louib/TStick/Eagle Libraries/PCB_board_20190523141823.png

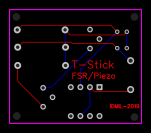
Eagle Libraries/PCB_board_20190523141823.png
