louib/TStick/Sopranino/2GW/FW19101/Docs/images/SopraninoJumperC-uC.jpg

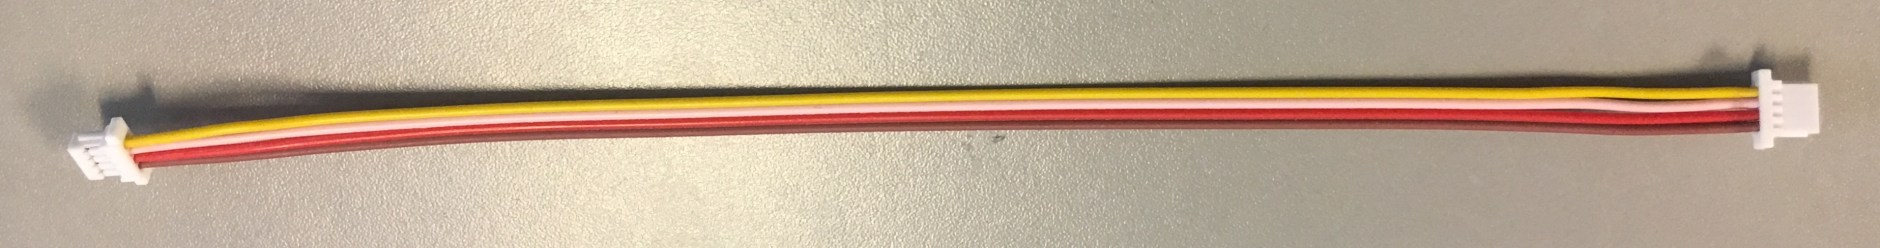
Sopranino/2GW/FW19101/Docs/images/SopraninoJumperC-uC.jpg
