louib/TStick/Sopranino/2GW/FW19101/Docs/MUMT620-t-stick_files/377761_352299741517825_1272722406_n.jpg

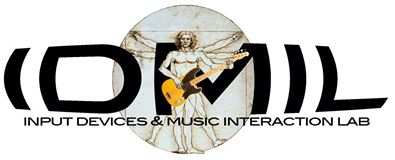
Sopranino/2GW/FW19101/Docs/MUMT620-t-stick_files/377761_352299741517825_1272722406_n.jpg
