louib/TStick/Sopranino/2GW/FW19101/Docs/MUMT620-t-stick_files/19886726_6071430966470_6630702371355754496_n.png.jpg

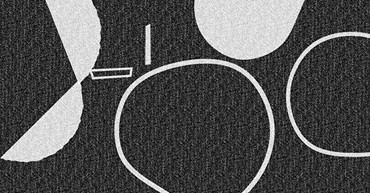
Sopranino/2GW/FW19101/Docs/MUMT620-t-stick_files/19886726_6071430966470_6630702371355754496_n.png.jpg
