louib/TStick/Sopranino/2GW/FW19101/Docs/MUMT620-t-stick_files/29963987_23842841834940019_1535957592986091520_n.png.jpg

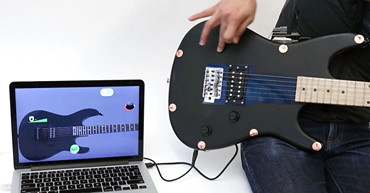
Sopranino/2GW/FW19101/Docs/MUMT620-t-stick_files/29963987_23842841834940019_1535957592986091520_n.png.jpg
