louib/TStick/Sopranino/2GW/FW19101/Docs/MUMT620-t-stick_files/SopraninoWiFi2019.jpg

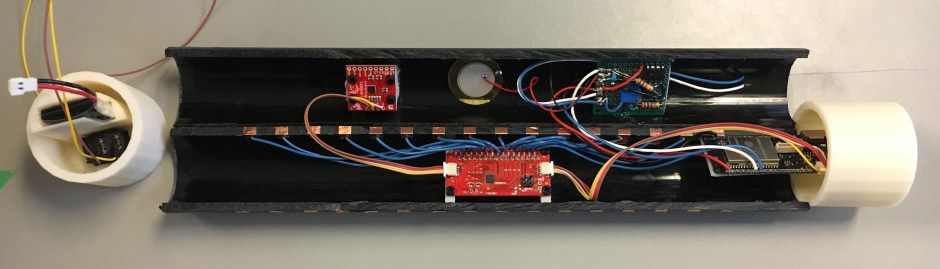
Sopranino/2GW/FW19101/Docs/MUMT620-t-stick_files/SopraninoWiFi2019.jpg
