louib/TStick/Sopranino/2G/172/Sopranino2G-172.sch

## EAGLE design Sopranino/2G/172/Sopranino2G-172.sch (2018-10-29)

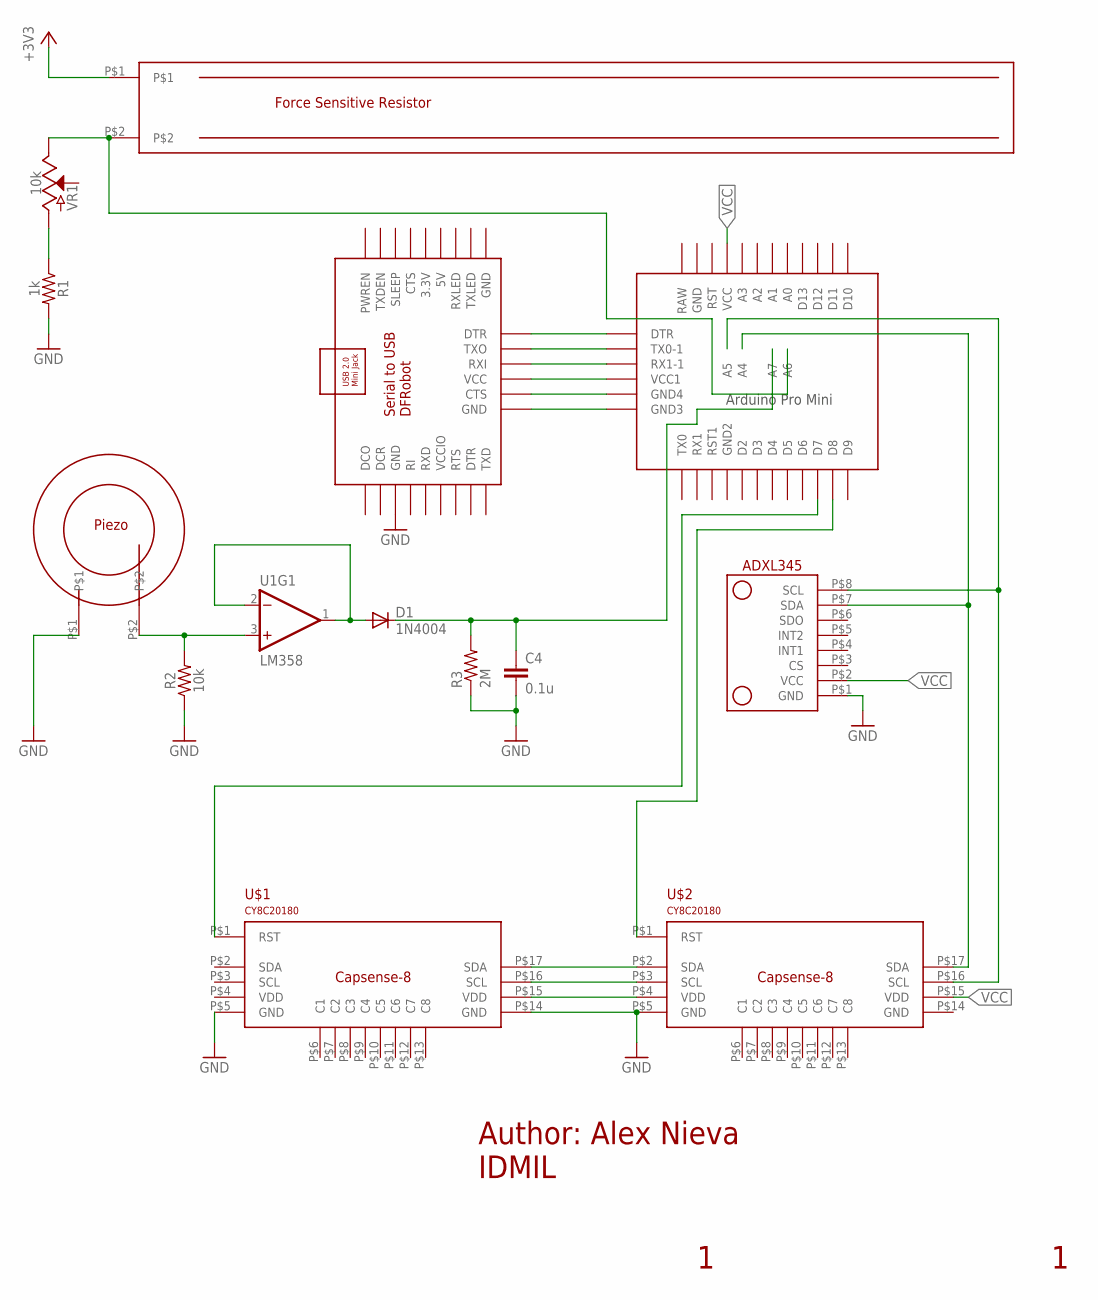
[picture p51: schematic Sopranino2G-172.sch]

Parts:
C4: 0.1u; C5B5.5
D1: 1N4004; DO41-10
R1: 1k; AXIAL-0.3
R2: 10k; AXIAL-0.3
R3: 2M; 0204/7
U1: LM358; DIP08
U$1, U$2: CAPSENSE-8
U$3: ADXL345
U$4: PRO-MINI-2
U$5: FSR_T-STICK
U$7: PIEZO_TSTICK
VR1: 10k; POT-PTH-ALPS

Connections:
+3V3: U$5.P$1
GND: C4.2, R1.P$2 (2), R2.P$1 (1), R3.1, U$1.P$5 (GND), U$1.P$14 (GND), U$2.P$5 (GND), U$3.P$1 (GND), U$7.P$1
unnamed: U$1.P$1 (RST), U$4.D7
unnamed: D1.A, U1.1 (OUT), U1.2 (-IN)
unnamed: U$1.P$17 (SDA), U$2.P$2 (SDA)
unnamed: U$2.P$1 (RST), U$4.D8
unnamed: U$1.P$16 (SCL), U$2.P$3 (SCL)
unnamed: U$1.P$15 (VDD), U$2.P$4 (VDD)
unnamed: R1.P$1 (1), VR1.P$3 (A)
unnamed: U$4.A6, U$5.P$2, VR1.P$1 (E)
unnamed: C4.1, D1.C, R3.2, U$4.A7
unnamed: R2.P$2 (2), U1.3 (+IN), U$7.P$2
SCL: U$2.P$16 (SCL), U$3.P$8 (SCL), U$4.A5
SDA: U$2.P$17 (SDA), U$3.P$7 (SDA), U$4.A4
VCC: U$2.P$15 (VDD), U$3.P$2 (VCC), U$4.VCC

Notes on the sheet:
Author: Alex Nieva IDMIL
