louib/TStick/Sopranino/2GW/FW19021/Sopranino2GW-181.sch

## EAGLE design Sopranino/2GW/FW19021/Sopranino2GW-181.sch (2018-10-29)

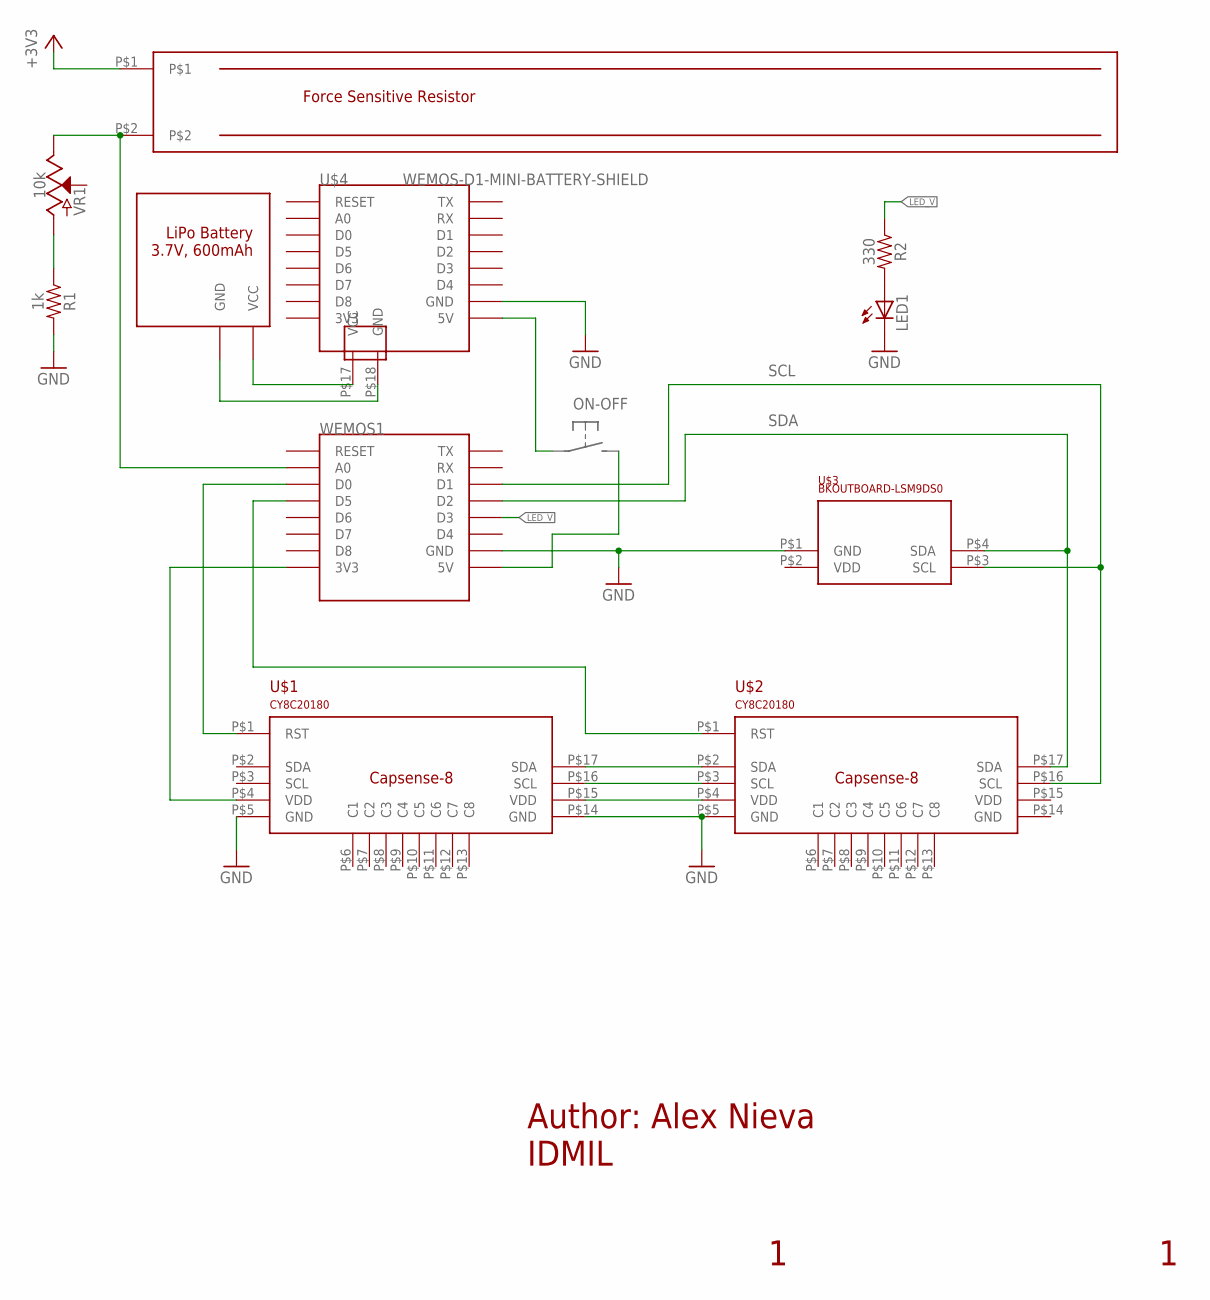
[picture p52: schematic Sopranino2GW-181.sch]

Parts:
LED1: LED3MM
R1: 1k; AXIAL-0.3
R2: 330; AXIAL-0.3
U$1, U$2: CAPSENSE-8
U$3: LSM9DS0_IDMIL_BKOUTBOARD
U$4: WEMOS-D1-MINI-BATTERY-SHIELD
U$5: FSR_T-STICK
VR1: 10k; POT-PTH-ALPS
WEMOS1: WEMOS-D1-MINI

Connections:
+3V3: U$5.P$1
GND: LED1.K (C), R1.P$2 (2), U$1.P$5 (GND), U$1.P$14 (GND), U$2.P$5 (GND), U$3.P$1 (GND), U$4.P$10 (GND), WEMOS1.GND
LED_V: R2.P$1 (1), WEMOS1.D3
unnamed: U$1.P$1 (RST), WEMOS1.D0
unnamed: U$2.P$1 (RST), WEMOS1.D5
unnamed: U$1.P$17 (SDA), U$2.P$2 (SDA)
unnamed: U$1.P$4 (VDD), WEMOS1.3V3
unnamed: U$1.P$16 (SCL), U$2.P$3 (SCL)
unnamed: U$1.P$15 (VDD), U$2.P$4 (VDD)
unnamed: LED1.A, R2.P$2 (2)
unnamed: R1.P$1 (1), VR1.P$3 (A)
unnamed: U$5.P$2, VR1.P$1 (E), WEMOS1.A0
SCL: U$2.P$16 (SCL), U$3.P$3 (SCL), WEMOS1.D1
SDA: U$2.P$17 (SDA), U$3.P$4 (SDA), WEMOS1.D2

Notes on the sheet:
Author: Alex Nieva IDMIL
