louib/TStick/Soprano/2G/024/Soprano2G-024.sch

## EAGLE design Soprano/2G/024/Soprano2G-024.sch (2018-10-29)

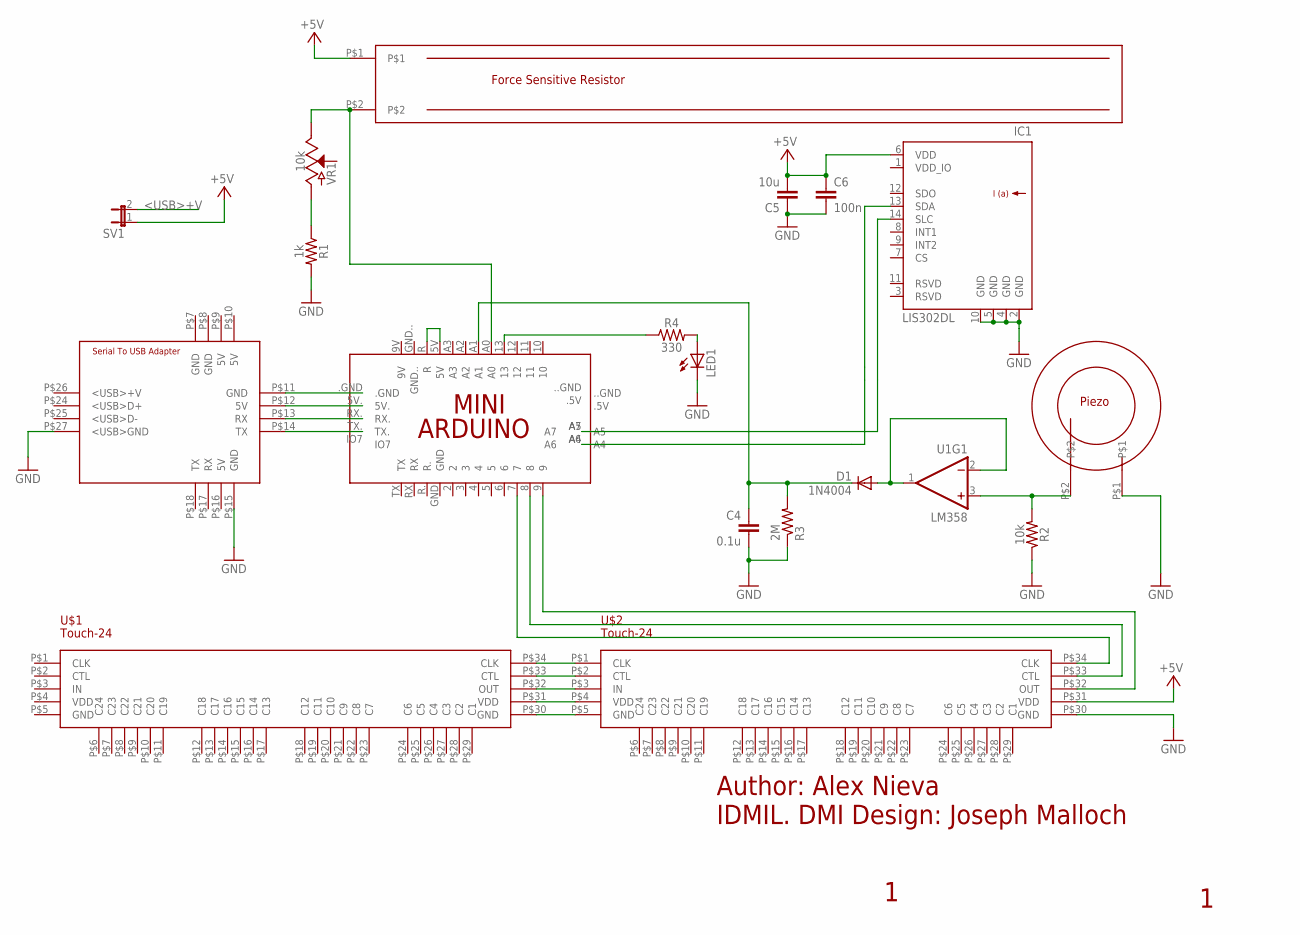
[picture p55: schematic Soprano2G-024.sch]

Parts:
C4: 0.1u; C5B5.5
C5: 10u; C5B5.5
C6: 100n; C5B5.5
D1: 1N4004; DO41-10
IC1: LIS302DL; LGA-14
LED1: LED3MM
PCB1: ARDUINO_MINI
R1: 1k; AXIAL-0.3
R2: 10k; AXIAL-0.3
R3: 2M; 0204/7
R4: 330; AXIAL-0.3
SV1: JP1E; JP1
U1: LM358; DIP08
U$1, U$2: TOUCH-24TOUCH-24; TOUCH24
U$4: SERIAL_TO_USB_ARDUINO_MINI; SERIAL_TO_USB_ARDUINO
U$5: FSR_T-STICK
U$6: PIEZO_TSTICK
VR1: 10k; POT-PTH-ALPS

Connections:
+5V: C5.2, C6.1, IC1.6 (VDD), PCB1.5V., SV1.1, U$2.P$31 (VDD), U$4.P$12 (5V), U$5.P$1
<USB>+V: SV1.2
GND: C4.2, C5.1, C6.2, IC1.2 (GND), IC1.4 (GND), IC1.5 (GND), IC1.10 (GND), LED1.K (C), R1.P$2 (2), R2.P$1 (1), R3.1, U$2.P$30 (GND), U$4.P$15 (GND), U$4.P$27 (<USB>GND), U$6.P$1
unnamed: U$1.P$34 (CLK), U$2.P$1 (CLK)
unnamed: U$1.P$33 (CTL), U$2.P$2 (CTL)
unnamed: U$1.P$32 (OUT), U$2.P$3 (IN)
unnamed: U$1.P$31 (VDD), U$2.P$4 (VDD)
unnamed: U$1.P$30 (GND), U$2.P$5 (GND)
unnamed: PCB1..GND, U$4.P$11 (GND)
unnamed: PCB1.RX., U$4.P$13 (RX)
unnamed: PCB1.TX., U$4.P$14 (TX)
unnamed: PCB1.13, R4.P$1 (1)
unnamed: LED1.A, R4.P$2 (2)
unnamed: R1.P$1 (1), VR1.P$3 (A)
unnamed: PCB1.A0, U$5.P$2, VR1.P$1 (E)
unnamed: D1.A, U1.1 (OUT), U1.2 (-IN)
unnamed: C4.1, D1.C, PCB1.A1, R3.2
unnamed: R2.P$2 (2), U1.3 (+IN), U$6.P$2
unnamed: PCB1.7, U$2.P$34 (CLK)
unnamed: PCB1.5V, PCB1.R
unnamed: PCB1.8, U$2.P$33 (CTL)
unnamed: PCB1.9, U$2.P$32 (OUT)
unnamed: IC1.13 (SDA), PCB1.A4
unnamed: IC1.14 (SLC), PCB1.A5

Notes on the sheet:
Author: Alex Nieva IDMIL. DMI Design: Joseph Malloch
