louib/TStick/Tenor/2G/014/Tenor2G-014.sch

## EAGLE design Tenor/2G/014/Tenor2G-014.sch (2018-10-29)

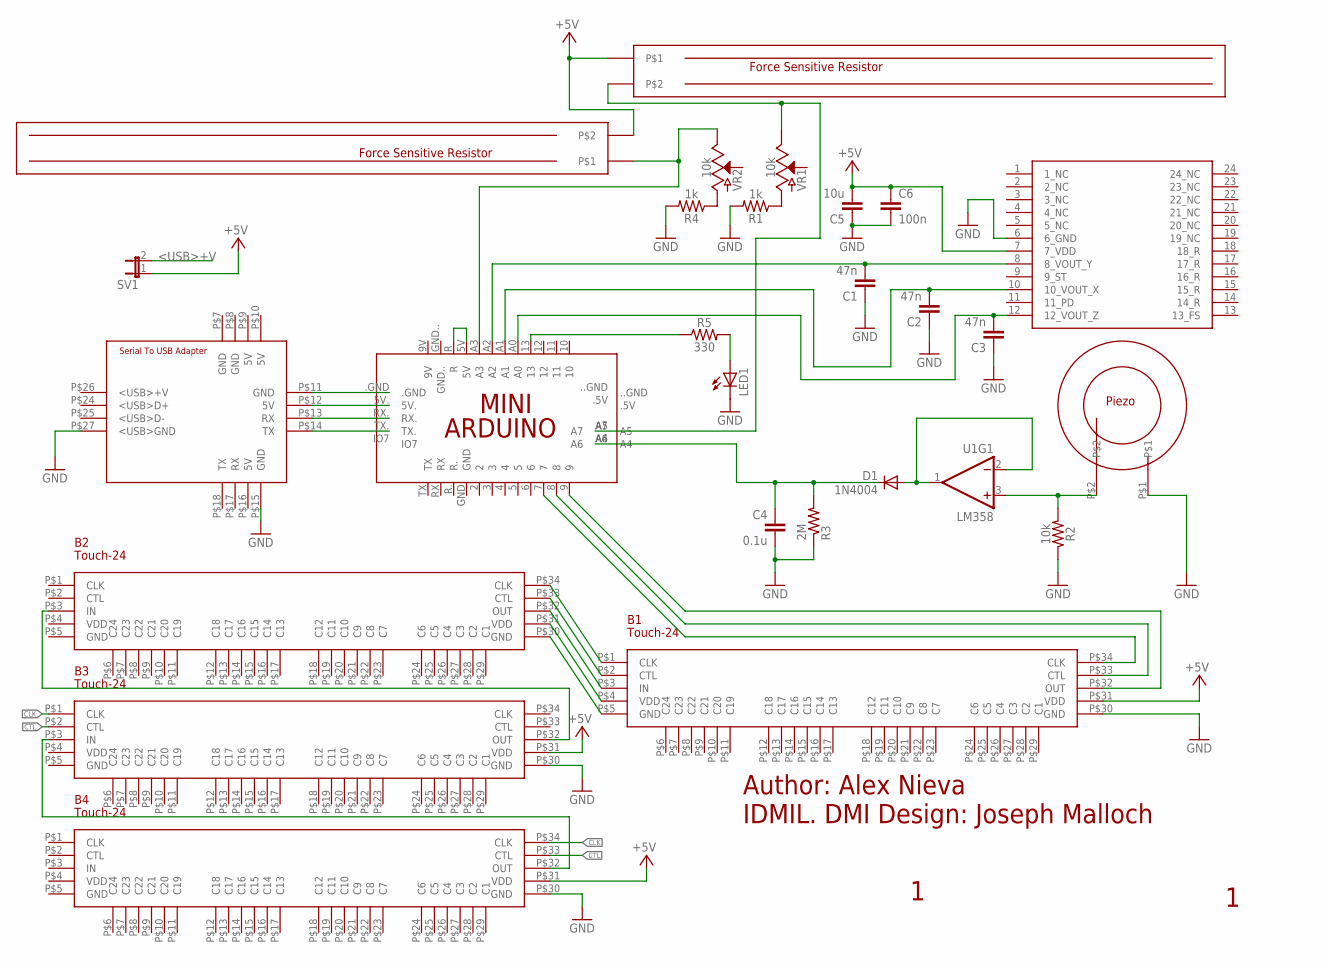
[picture p57: schematic Tenor2G-014.sch]

Parts:
B1, B2, B3, B4: TOUCH-24TOUCH-24; TOUCH24
C1, C2, C3: 47n; C5B5.5
C4: 0.1u; C5B5.5
C5: 10u; C5B5.5
C6: 100n; C5B5.5
D1: 1N4004; DO41-10
LED1: LED3MM
PCB1: ARDUINO_MINI
R1, R4: 1k; AXIAL-0.3
R2: 10k; AXIAL-0.3
R3: 2M; 0204/7
R5: 330; AXIAL-0.3
SV1: JP1E; JP1
U1: LM358; DIP08
U$3: LIS3L02AS4; SO-24
U$4: SERIAL_TO_USB_ARDUINO_MINI; SERIAL_TO_USB_ARDUINO
U$6: PIEZO_TSTICK
VR1, VR2: 10k; POT-PTH-ALPS

Connections:
+5V: B1.P$31 (VDD), B3.P$31 (VDD), B4.P$31 (VDD), C5.2, C6.1, PCB1.5V., SV1.1, U$3.7 (7_VDD), U$4.P$12 (5V)
<USB>+V: SV1.2
CLK: B3.P$1 (CLK), B4.P$34 (CLK)
CTL: B3.P$2 (CTL), B4.P$33 (CTL)
GND: B1.P$30 (GND), B3.P$30 (GND), B4.P$30 (GND), C1.1, C2.1, C3.1, C4.2, C5.1, C6.2, LED1.K (C), R1.P$2 (2), R2.P$1 (1), R3.1, R4.P$2 (2), U$3.6 (6_GND), U$4.P$15 (GND), U$4.P$27 (<USB>GND), U$6.P$1
unnamed: B1.P$1 (CLK), B2.P$34 (CLK)
unnamed: B1.P$2 (CTL), B2.P$33 (CTL)
unnamed: B1.P$3 (IN), B2.P$32 (OUT)
unnamed: B1.P$4 (VDD), B2.P$31 (VDD)
unnamed: B1.P$5 (GND), B2.P$30 (GND)
unnamed: PCB1..GND, U$4.P$11 (GND)
unnamed: C3.2, PCB1.A0, U$3.12 (12_VOUT_Z)
unnamed: PCB1.RX., U$4.P$13 (RX)
unnamed: PCB1.TX., U$4.P$14 (TX)
unnamed: R4.P$1 (1), VR2.P$3 (A)
unnamed: PCB1.A7, VR1.P$1 (E)
unnamed: R1.P$1 (1), VR1.P$3 (A)
unnamed: B2.P$3 (IN), B3.P$32 (OUT)
unnamed: D1.A, U1.1 (OUT), U1.2 (-IN)
unnamed: C4.1, D1.C, PCB1.A6, R3.2
unnamed: R2.P$2 (2), U1.3 (+IN), U$6.P$2
unnamed: B1.P$34 (CLK), PCB1.7
unnamed: PCB1.5V, PCB1.R
unnamed: B1.P$33 (CTL), PCB1.8
unnamed: B1.P$32 (OUT), PCB1.9
unnamed: PCB1.A3, VR2.P$1 (E)
unnamed: C1.2, PCB1.A2, U$3.8 (8_VOUT_Y)
unnamed: C2.2, PCB1.A1, U$3.10 (10_VOUT_X)
unnamed: B3.P$3 (IN), B4.P$32 (OUT)
unnamed: LED1.A, R5.P$2 (2)
unnamed: PCB1.13, R5.P$1 (1)

Notes on the sheet:
Author: Alex Nieva IDMIL. DMI Design: Joseph Malloch
